andresv/switch-boosterpack/firmware/switch/CourierNew_14x15.h

#ifndef COURIERNEW_14X15_H_
#define COURIERNEW_14X15_H_


/*******************************************************************************************
  Font name: Courier New
  Font width: 14 (monospaced font)
  Font height: 15
  Encode: Unicode

  Data length: 8 bits
  Data format: Big Endian, Column based, Row preferred, Unpacked
 *******************************************************************************************/

const unsigned char font_table_large[] = {

/* character 0x0020 (' '): (width=14, offset=0) */
0x00, 0x00, 0x00, 0x00, 0x00, 0x00, 0x00, 0x00, 
0x00, 0x00, 0x00, 0x00, 0x00, 0x00, 0x00, 0x00, 
0x00, 0x00, 0x00, 0x00, 0x00, 0x00, 0x00, 0x00, 
0x00, 0x00, 0x00, 0x00, 

/* character 0x0021 ('!'): (width=14, offset=28) */
0x00, 0x00, 0x00, 0x00, 0x00, 0x00, 0x00, 0xFF, 
0x00, 0x00, 0x00, 0x00, 0x00, 0x00, 0x00, 0x00, 
0x00, 0x00, 0x00, 0x00, 0x06, 0xC6, 0x06, 0x00, 
0x00, 0x00, 0x00, 0x00, 

/* character 0x0022 ('"'): (width=14, offset=56) */
0x00, 0x00, 0x00, 0xE0, 0xFE, 0xE0, 0x00, 0x00, 
0xE0, 0xFE, 0xE0, 0x00, 0x00, 0x00, 0x00, 0x00, 
0x00, 0x00, 0x00, 0x00, 0x00, 0x00, 0x00, 0x00, 
0x00, 0x00, 0x00, 0x00, 

/* character 0x0023 ('#'): (width=14, offset=84) */
0x00, 0x00, 0x04, 0x04, 0x04, 0x3F, 0xC4, 0x04, 
0x04, 0x3F, 0xC4, 0x04, 0x04, 0x00, 0x00, 0x00, 
0x20, 0x20, 0x22, 0xFC, 0x20, 0x20, 0x22, 0xFC, 
0x20, 0x20, 0x20, 0x00, 

/* character 0x0024 ('$'): (width=14, offset=112) */
0x00, 0x00, 0x00, 0x1C, 0x22, 0x42, 0x41, 0xC1, 
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
0x02, 0x7C, 0x80, 0x00, 

/* character 0x0078 ('x'): (width=14, offset=2464) */
0x00, 0x00, 0x08, 0x0C, 0x0A, 0x09, 0x00, 0x00, 
0x09, 0x0A, 0x0C, 0x08, 0x00, 0x00, 0x00, 0x02, 
0x06, 0x0A, 0x12, 0x20, 0xC0, 0xC0, 0x20, 0x12, 
0x0A, 0x06, 0x02, 0x00, 

/* character 0x0079 ('y'): (width=14, offset=2492) */
0x00, 0x00, 0xC0, 0x30, 0x0E, 0x01, 0x00, 0x01, 
0x0E, 0x30, 0xC0, 0x00, 0x00, 0x00, 0x00, 0x02, 
0x02, 0x02, 0x06, 0x9A, 0x62, 0x80, 0x00, 0x00, 
0x00, 0x00, 0x00, 0x00, 

/* character 0x007A ('z'): (width=14, offset=2520) */
0x00, 0x00, 0x00, 0x0E, 0x08, 0x08, 0x08, 0x08, 
0x08, 0x09, 0x0A, 0x0C, 0x00, 0x00, 0x00, 0x00, 
0x00, 0x06, 0x0A, 0x12, 0x22, 0x42, 0x82, 0x02, 
0x02, 0x0E, 0x00, 0x00, 

};

#endif /*COURIERNEW_14X15_H_*/
