andresv/switch-boosterpack/firmware/switch/CourierNew_5x7.h

#ifndef COURIERNEW_5X7_H_
#define COURIERNEW_5X7_H_

const unsigned char font_table_small[] = {

/* character 0x0020 (' '): (width=5, offset=0) */
0x00, 0x00, 0x00, 0x00, 0x00, 

/* character 0x0021 ('!'): (width=5, offset=5) */
0x00, 0x00, 0x00, 0xFA, 0x00, 

/* character 0x0022 ('"'): (width=5, offset=10) */
0x00, 0x80, 0x00, 0x80, 0x00, 

/* character 0x0023 ('#'): (width=5, offset=15) */
0x48, 0xFE, 0x48, 0xFE, 0x48, 

/* character 0x0024 ('$'): (width=5, offset=20) */
0x00, 0x60, 0x54, 0xFE, 0x5C, 

/* character 0x0025 ('%'): (width=5, offset=25) */
0xC2, 0xCC, 0xFE, 0xCA, 0x8E, 

/* character 0x0026 ('&'): (width=5, offset=30) */
0x00, 0x1E, 0xE2, 0xBA, 0xC6, 

/* character 0x0027 ('''): (width=5, offset=35) */
0x00, 0x00, 0x80, 0x00, 0x00, 

/* character 0x0028 ('('): (width=5, offset=40) */
0x00, 0x00, 0xFC, 0x02, 0x00, 

/* character 0x0029 (')'): (width=5, offset=45) */
0x00, 0x00, 0x02, 0xFC, 0x00, 

/* character 0x002A ('*'): (width=5, offset=50) */
0x00, 0x28, 0x70, 0x78, 0x30, 

/* character 0x002B ('+'): (width=5, offset=55) */
0x00, 0x10, 0x10, 0x78, 0x10, 

/* character 0x002C (','): (width=5, offset=60) */
0x00, 0x00, 0x00, 0x06, 0x00, 

/* character 0x002D ('-'): (width=5, offset=65) */
0x00, 0x10, 0x10, 0x10, 0x10, 

/* character 0x002E ('.'): (width=5, offset=70) */
0x00, 0x00, 0x02, 0x00, 0x00, 

/* character 0x002F ('/'): (width=5, offset=75) */
0x00, 0x06, 0x18, 0x60, 0x80, 

/* character 0x0030 ('0'): (width=5, offset=80) */
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

/* character 0x0078 ('x'): (width=5, offset=440) */
0x42, 0x3C, 0x1C, 0x66, 0x00, 

/* character 0x0079 ('y'): (width=5, offset=445) */
0x00, 0x60, 0x1C, 0x1E, 0x60, 

/* character 0x007A ('z'): (width=5, offset=450) */
0x00, 0x42, 0x4E, 0x72, 0x42, 
};

#endif /*COURIERNEW_5X7_H_*/
